ssokolow/ventilomatic/img/parts/3_standoffs.jpg

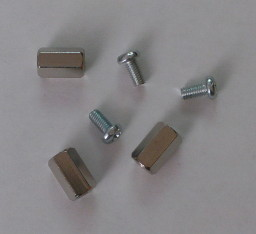
img/parts/3_standoffs.jpg
