ssokolow/ventilomatic/img/parts/breadboard.jpg

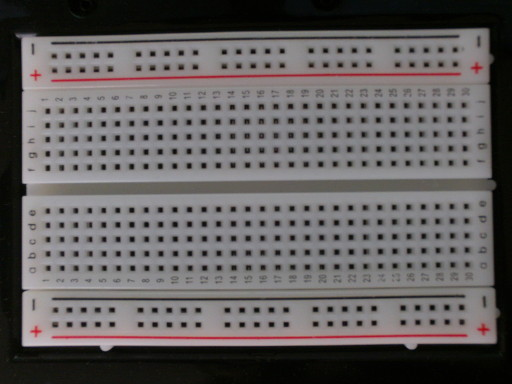
img/parts/breadboard.jpg
