ssokolow/ventilomatic/img/parts/cat5_patch.jpg

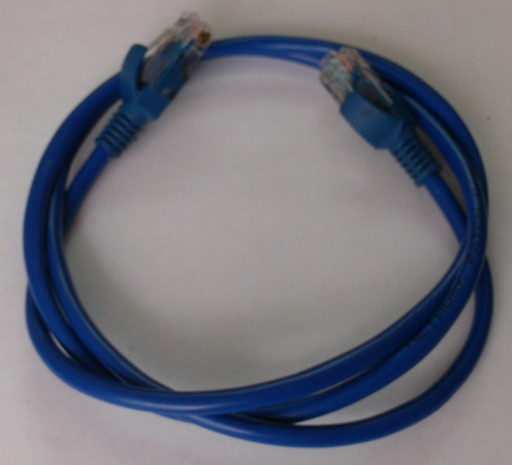
img/parts/cat5_patch.jpg
