ssokolow/ventilomatic/img/parts/cds_cell.jpg

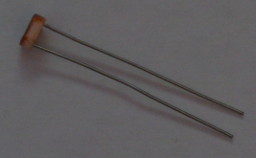
img/parts/cds_cell.jpg
