ssokolow/ventilomatic/img/parts/cm19a.jpg

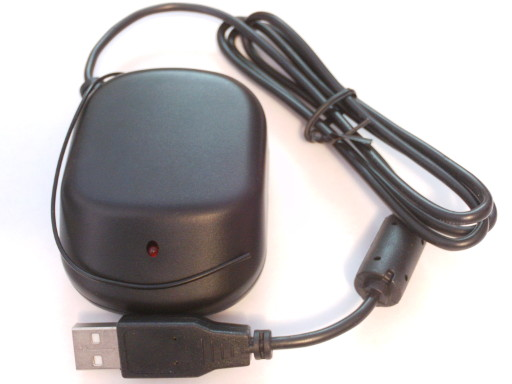
img/parts/cm19a.jpg
