ssokolow/ventilomatic/img/parts/dht22.jpg

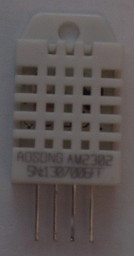
img/parts/dht22.jpg
