ssokolow/ventilomatic/img/parts/enc28j60_module.jpg

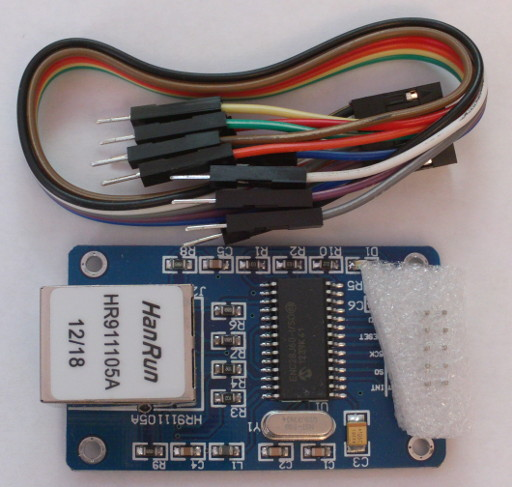
img/parts/enc28j60_module.jpg
