ssokolow/ventilomatic/img/parts/freaduino_leonardo.jpg

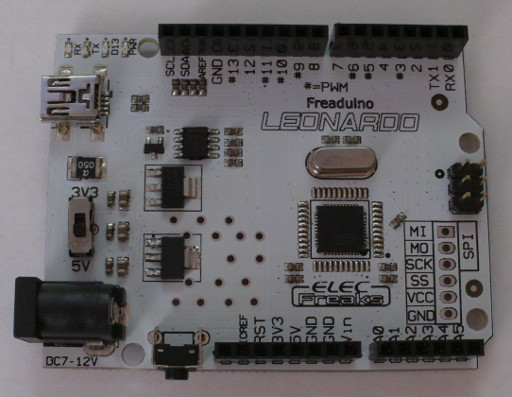
img/parts/freaduino_leonardo.jpg
