ssokolow/ventilomatic/img/parts/m-f_spacers.jpg

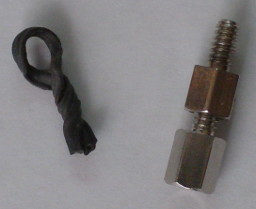
img/parts/m-f_spacers.jpg
