ssokolow/ventilomatic/img/parts/prototyping_shield.jpg

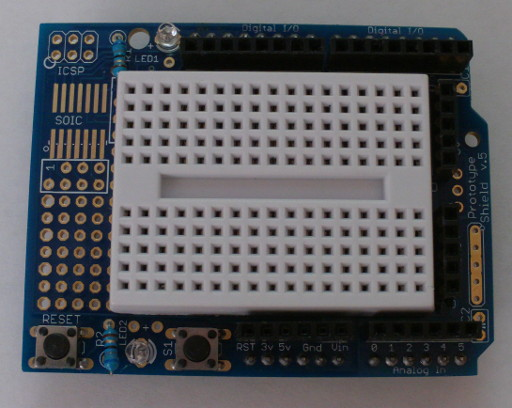
img/parts/prototyping_shield.jpg
