ssokolow/ventilomatic/img/parts/psu_1.jpg

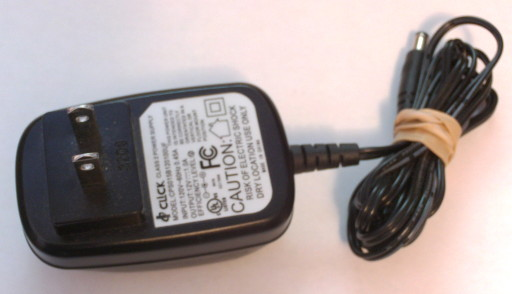
img/parts/psu_1.jpg
