ssokolow/ventilomatic/img/parts/psu_2.jpg

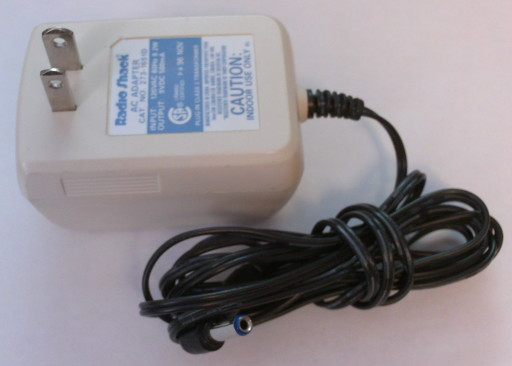
img/parts/psu_2.jpg
