ssokolow/ventilomatic/img/parts/psu_3.jpg

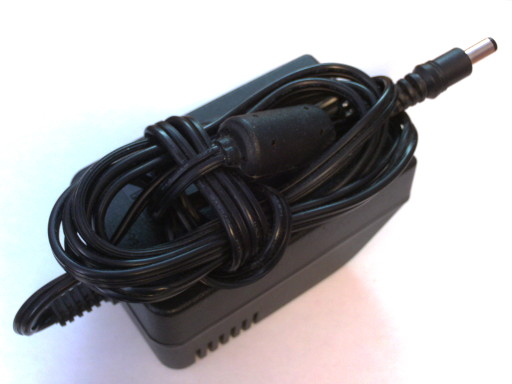
img/parts/psu_3.jpg
