ssokolow/ventilomatic/img/parts/raspberry_pi.jpg

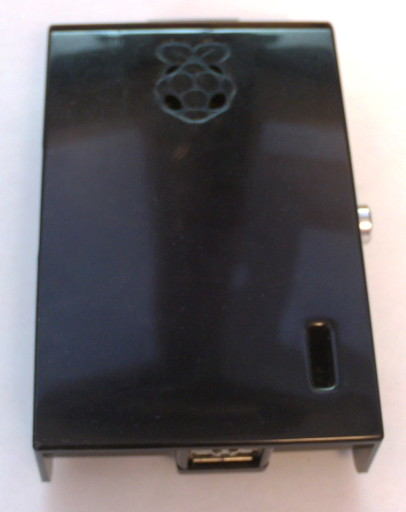
img/parts/raspberry_pi.jpg
