ssokolow/ventilomatic/img/parts/redboard.jpg

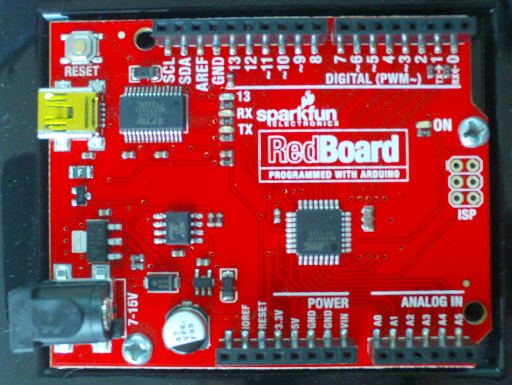
img/parts/redboard.jpg
