ssokolow/ventilomatic/img/parts/sd_card.jpg

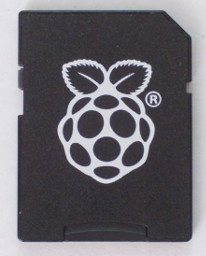
img/parts/sd_card.jpg
