ssokolow/ventilomatic/img/parts/short_usb_mini.jpg

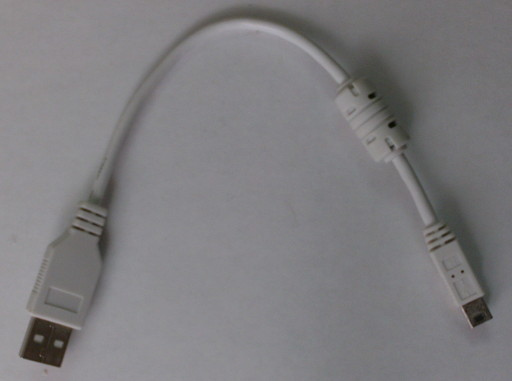
img/parts/short_usb_mini.jpg
