ssokolow/ventilomatic/img/parts/stacking_headers.jpg

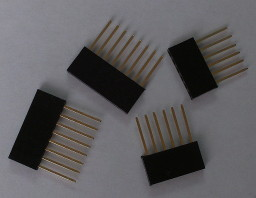
img/parts/stacking_headers.jpg
