ssokolow/ventilomatic/img/assembled/leonardo_node.jpg

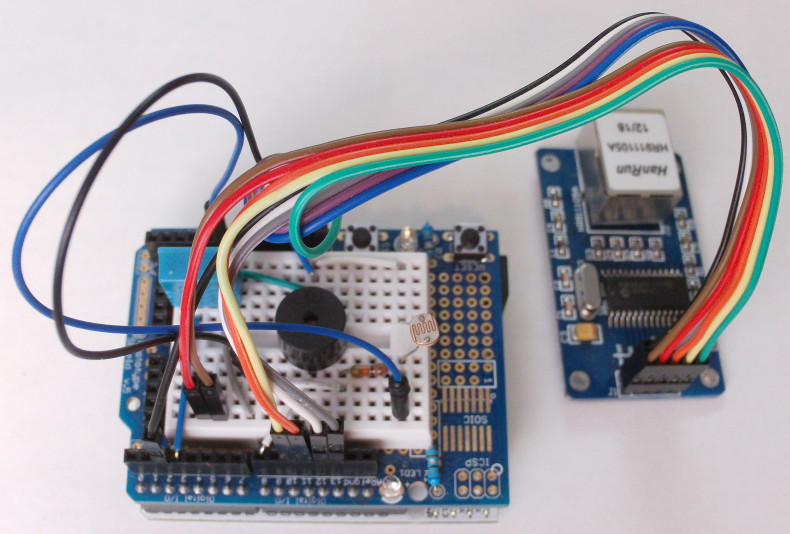
img/assembled/leonardo_node.jpg
