ssokolow/ventilomatic/img/assembled/redboard_node.jpg

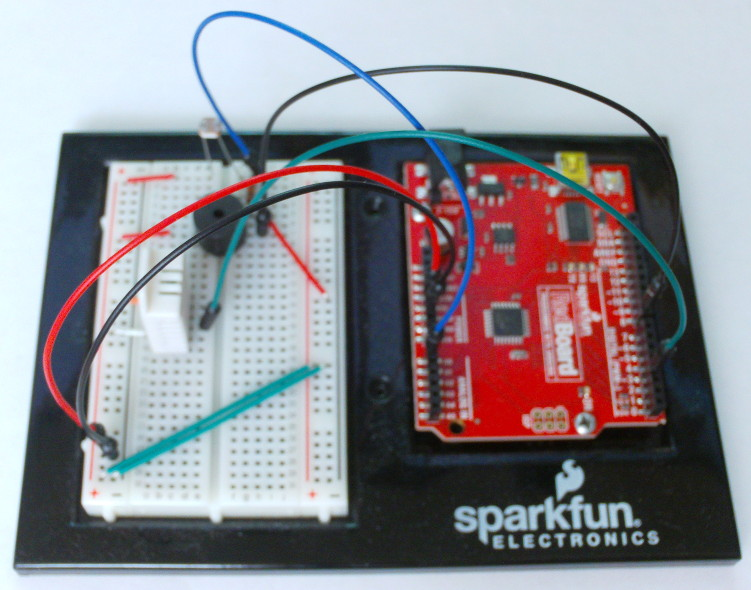
img/assembled/redboard_node.jpg
