ssokolow/ventilomatic/img/assembled/sensor_node_bb.png

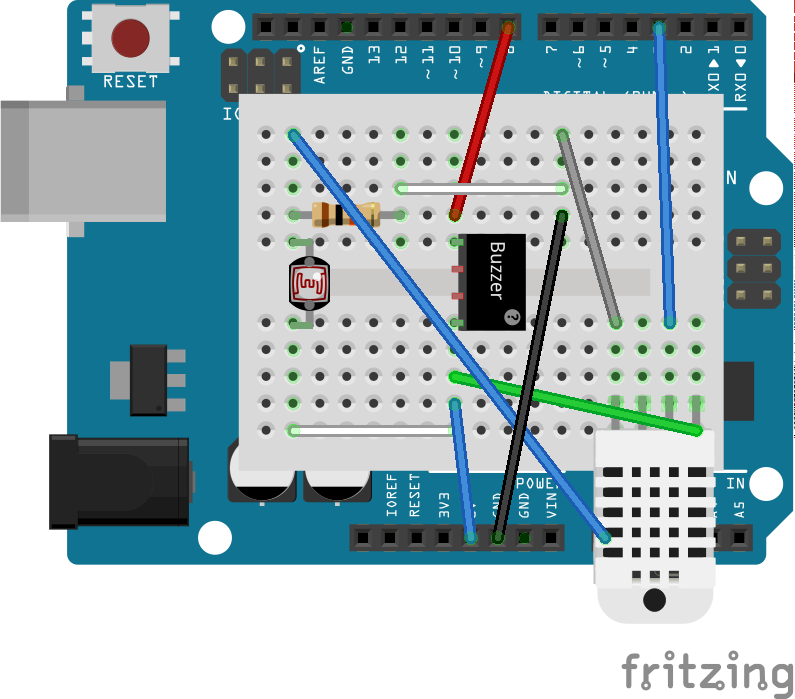
img/assembled/sensor_node_bb.png
