ssokolow/ventilomatic/img/assembled/uno_node.jpg

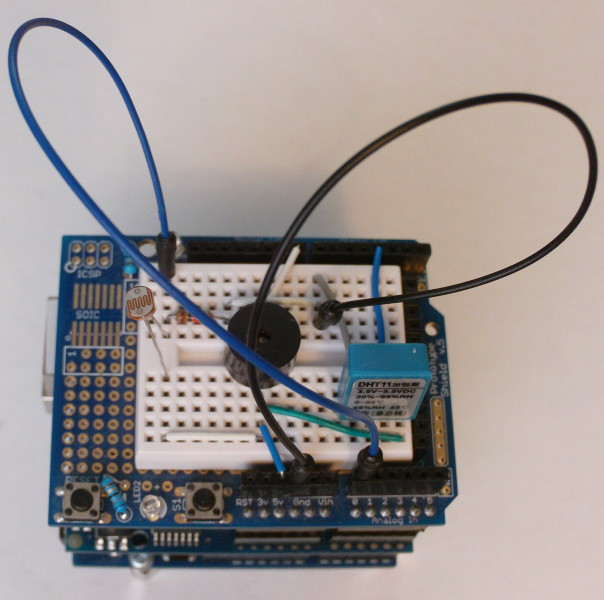
img/assembled/uno_node.jpg
